cese-dci/tpfinal-leonardods18/Objeto_3d/Captura2.JPG

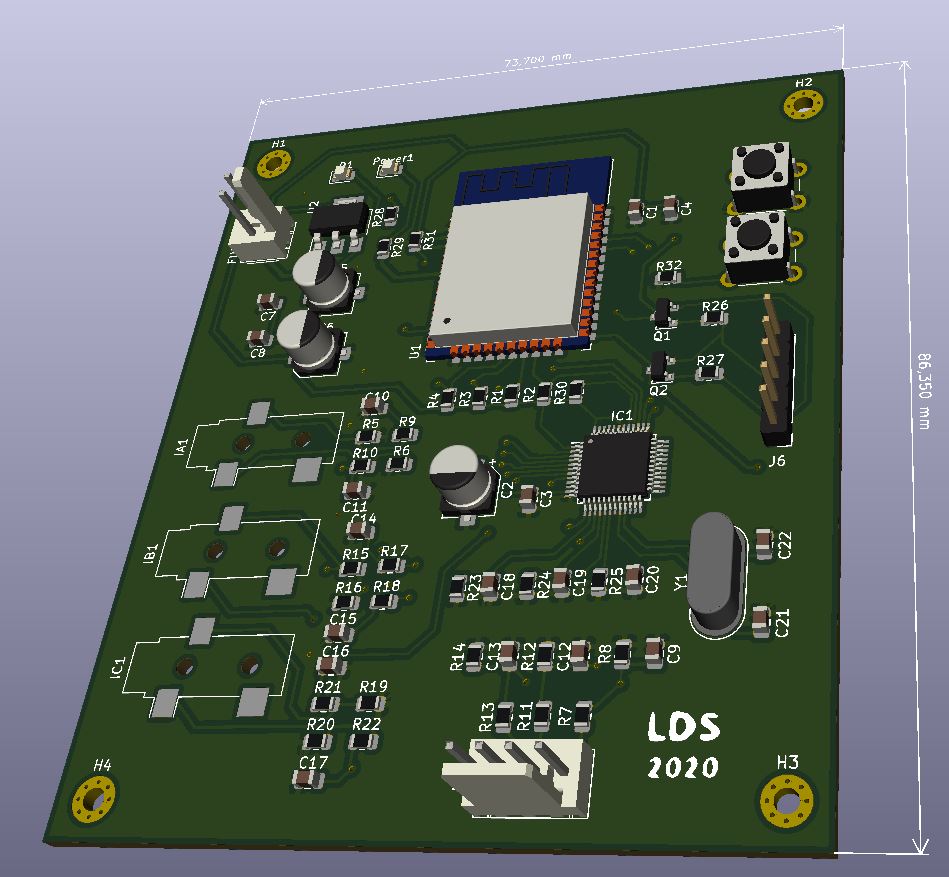
Objeto_3d/Captura2.JPG
